karnadii/geulis/case/geulis_v3_1.5mm_bening.dxf

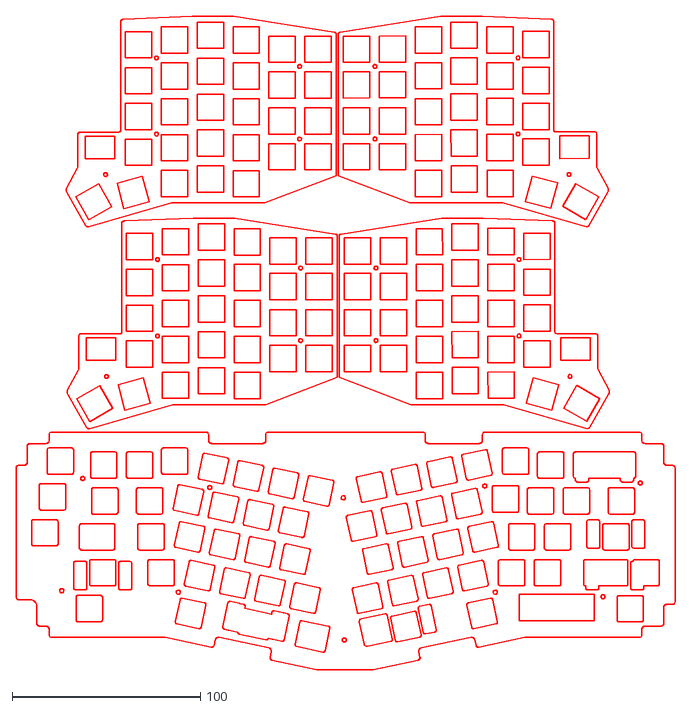
[picture p21: CAD file, 2021-08-16]
case/geulis_v3_1.5mm_bening.dxf
349.8 x 346.8
