karnadii/geulis/case/geulisv2_3mm_merah_bening.dxf

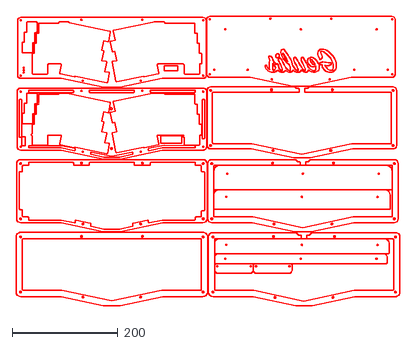
[picture p22: CAD file, 2021-08-16]
case/geulisv2_3mm_merah_bening.dxf
725.5 x 547.1
