karnadii/geulis/case/geulis_1.5mm_bening.dxf

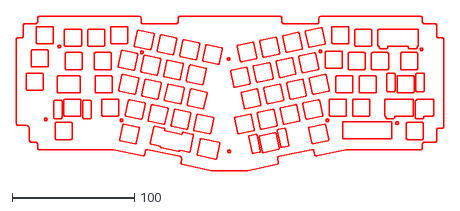
[picture p23: CAD file, 2021-08-16]
case/geulis_1.5mm_bening.dxf
349.8 x 126.0
