karnadii/geulis/case/geulis_plate_for_geulis_case.dxf

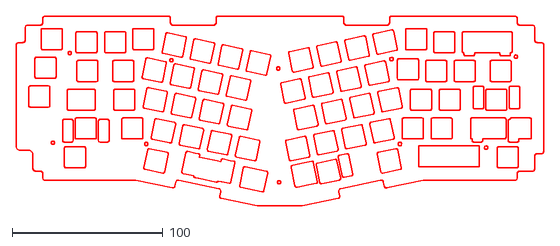
[picture p24: CAD file, 2021-08-16]
case/geulis_plate_for_geulis_case.dxf
349.8 x 126.0
