karnadii/geulis/case/geulis_v5_3mm_merah_transparan.dxf

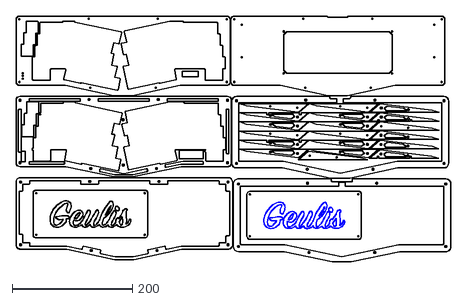
[picture p25: CAD file, 2021-08-16]
case/geulis_v5_3mm_merah_transparan.dxf
723.5 x 409.1
