karnadii/geulis/case/geulis_v5_1.5mm.dxf

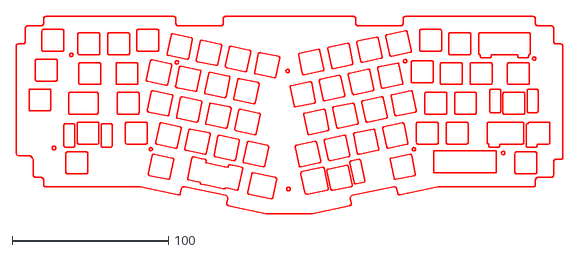
[picture p26: CAD file, 2021-08-16]
case/geulis_v5_1.5mm.dxf
349.8 x 126.0
