karnadii/geulis/case/geulis_2mm_frosted.dxf

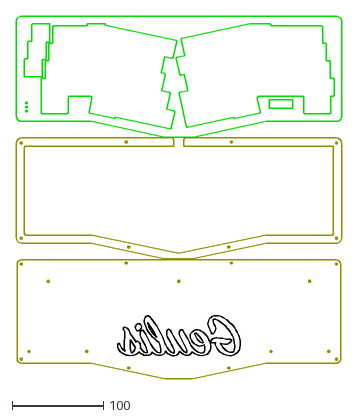
[picture p27: CAD file, 2021-08-16]
case/geulis_2mm_frosted.dxf
356.4 x 397.1
