karnadii/geulis/case/geulis_3mm_frosted.dxf

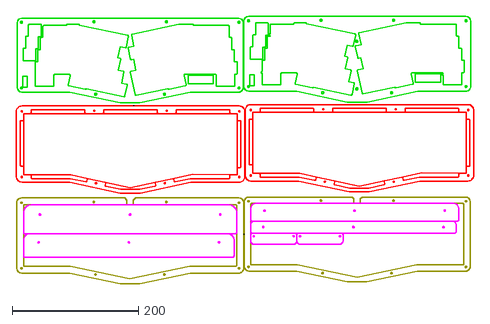
[picture p28: CAD file, 2021-08-16]
case/geulis_3mm_frosted.dxf
725.5 x 424.8
